cyberboy666/_transcribe_/software/src/midievents.h

namespace MIDINOTE{

    const uint8_t C4 = 60;
    const uint8_t C4SHARP = 61;

}

namespace MIDICOMMAND{
    const uint8_t NOTEON = 144;
    const uint8_t CC = 176;
}

namespace INTYPE{
    const uint8_t NOTE = 0;
    const uint8_t CCVALUE = 1;
}
